mdomingo2/tennixx_locker/renders/label_demo.png

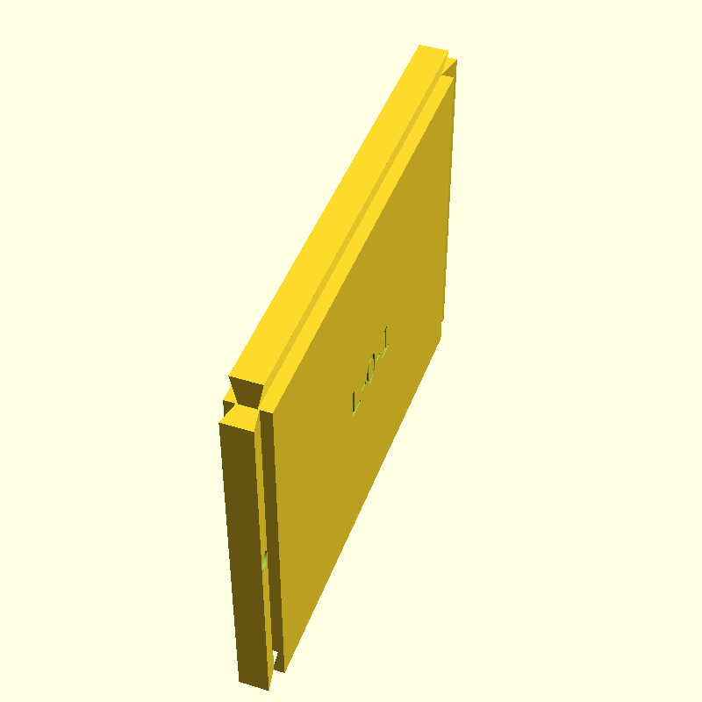
renders/label_demo.png
