mdomingo2/tennixx_locker/renders/tile_bottom_11.png

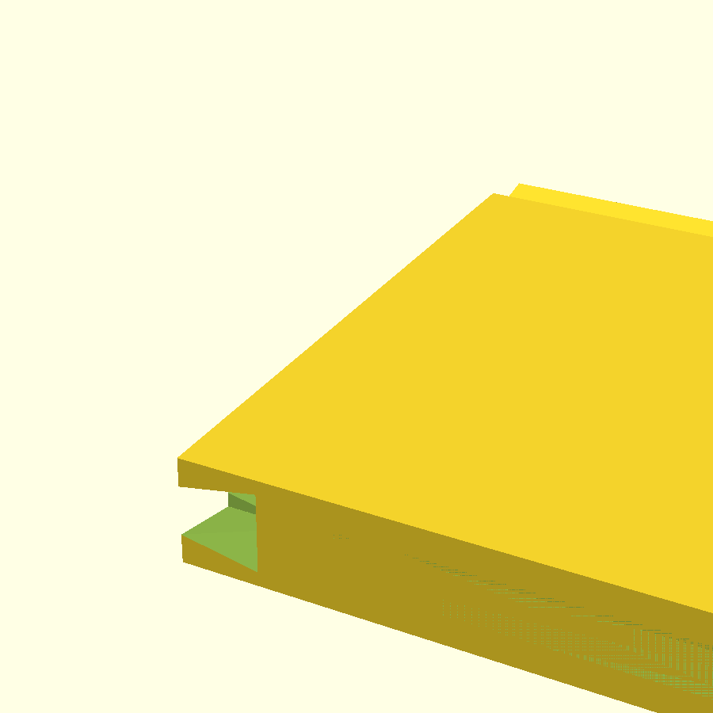
renders/tile_bottom_11.png
