mdomingo2/tennixx_locker/stl/top_1_0.stl

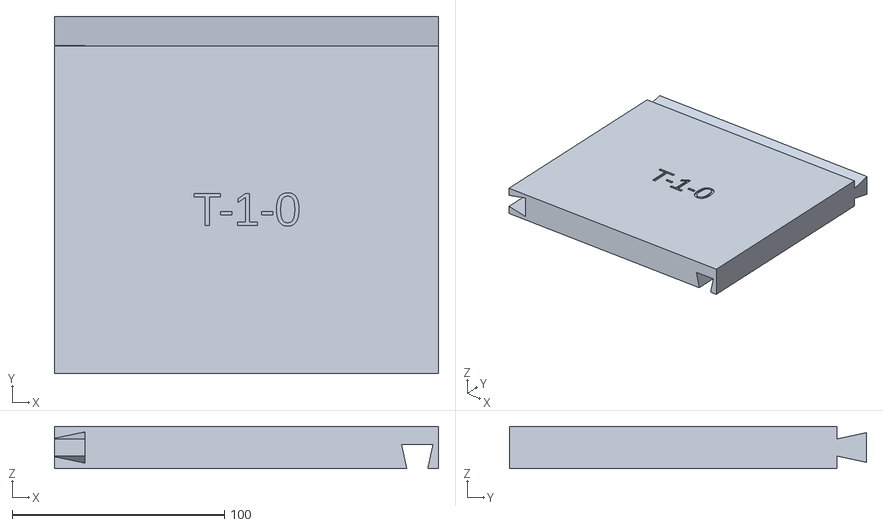
[picture p26: CAD file, 2026-06-09]
stl/top_1_0.stl
180.9 x 168.3 x 20.0
