mdomingo2/tennixx_locker/stl/bottom_1_1.stl

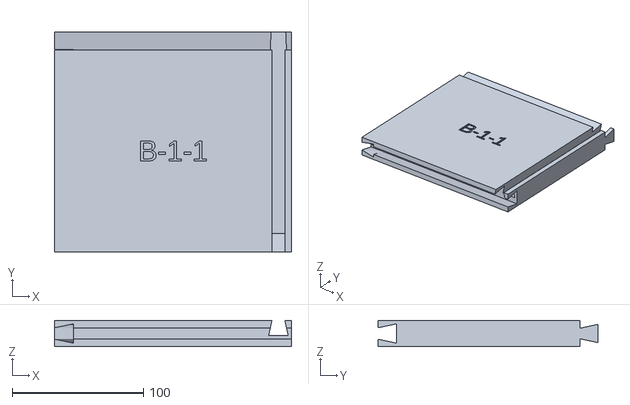
[picture p27: CAD file, 2026-06-09]
stl/bottom_1_1.stl
180.9 x 168.3 x 20.0
