mdomingo2/tennixx_locker/stl/back_1_1.stl

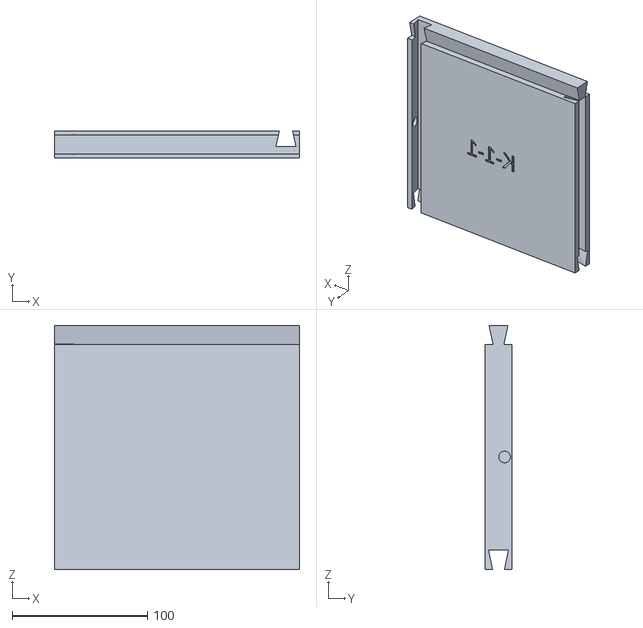
[picture p28: CAD file, 2026-06-09]
stl/back_1_1.stl
180.9 x 20.0 x 180.3
