mdomingo2/tennixx_locker/stl/back_0_1.stl

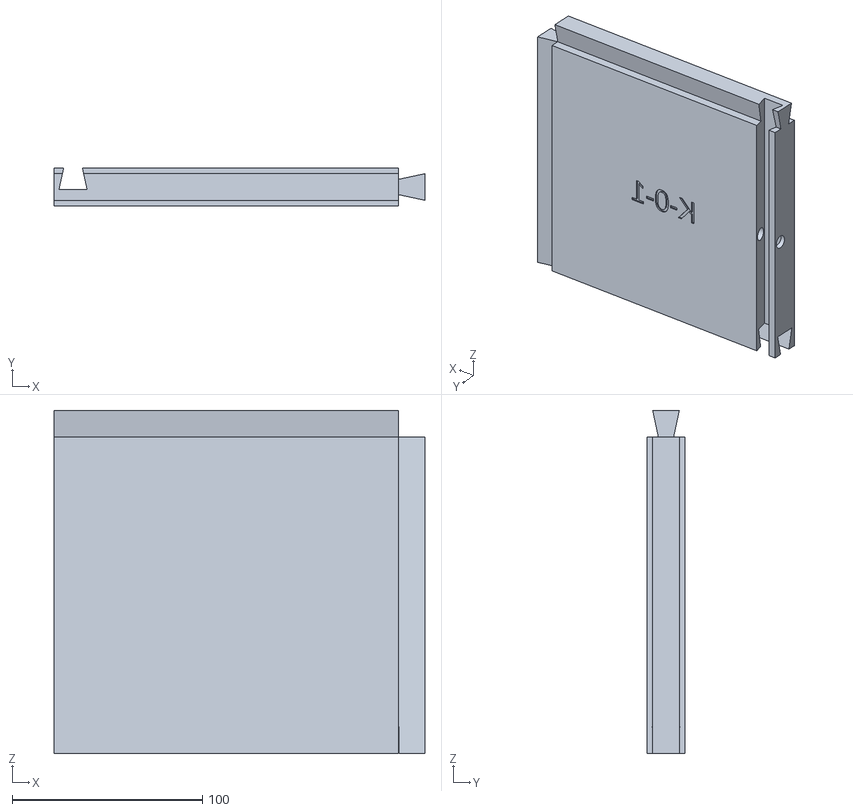
[picture p29: CAD file, 2026-06-09]
stl/back_0_1.stl
194.9 x 20.0 x 180.3
